cojanuteodor/Voltage-Regulator-with-Series-Pass-Element/Simulations/DOMENIU_DE_TEMP_LA_VO_MAX.png

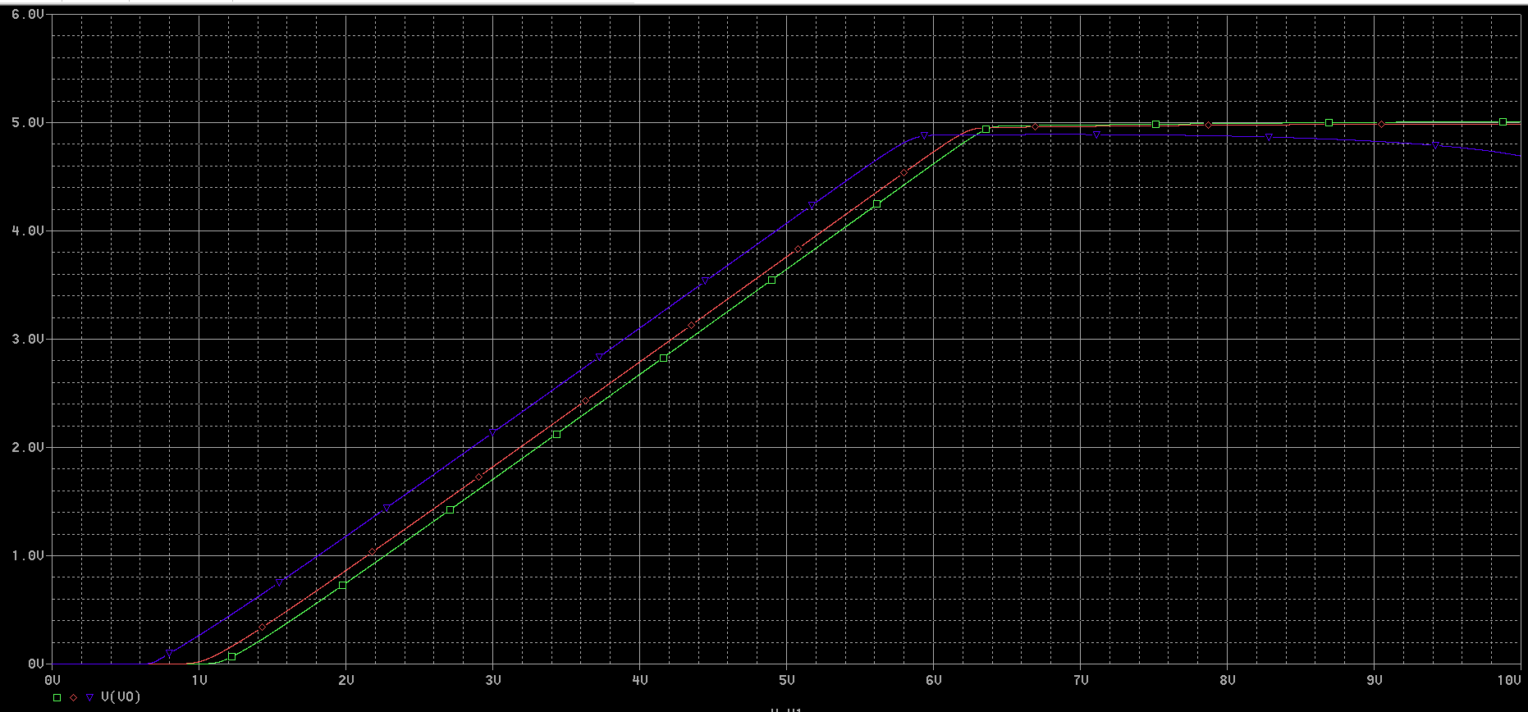
Simulations/DOMENIU_DE_TEMP_LA_VO_MAX.png
