cojanuteodor/Voltage-Regulator-with-Series-Pass-Element/Simulations/DOMENIU_DE_TEMP_VO_MIN.png

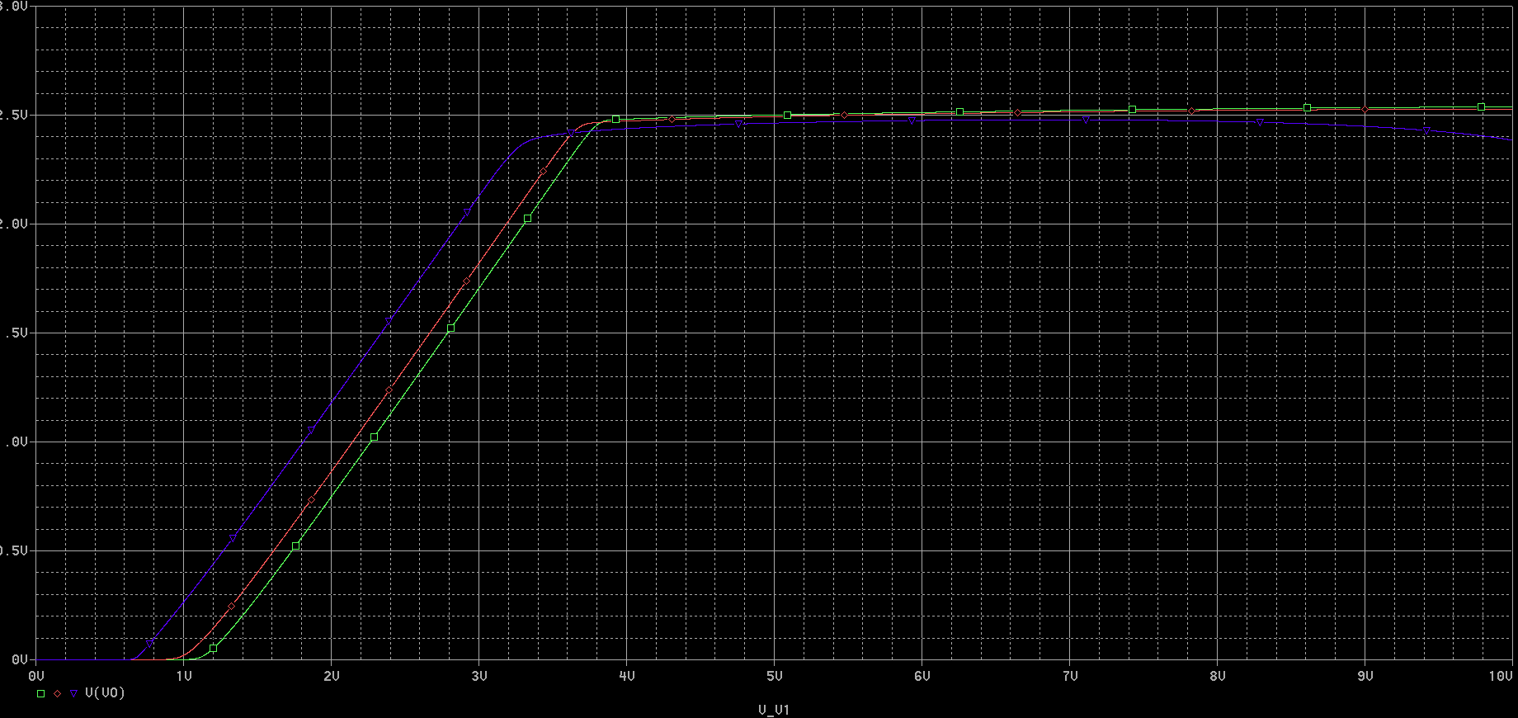
Simulations/DOMENIU_DE_TEMP_VO_MIN.png
