cojanuteodor/Voltage-Regulator-with-Series-Pass-Element/Simulations/PROTECTIA_TERMICA_LA_VO_MIN.png

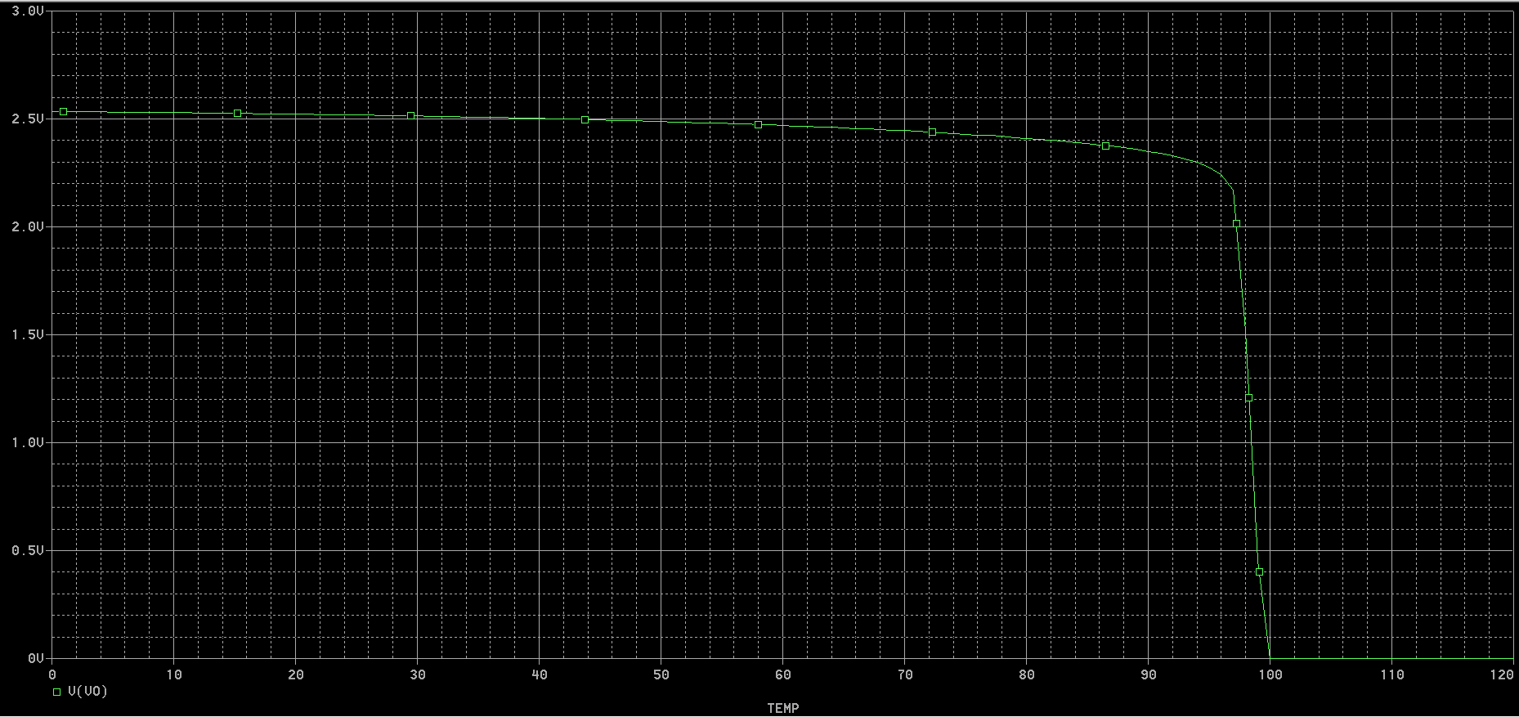
Simulations/PROTECTIA_TERMICA_LA_VO_MIN.png
