cojanuteodor/Voltage-Regulator-with-Series-Pass-Element/Simulations/PROTECTIA_TERMICA_VO_MAX.png

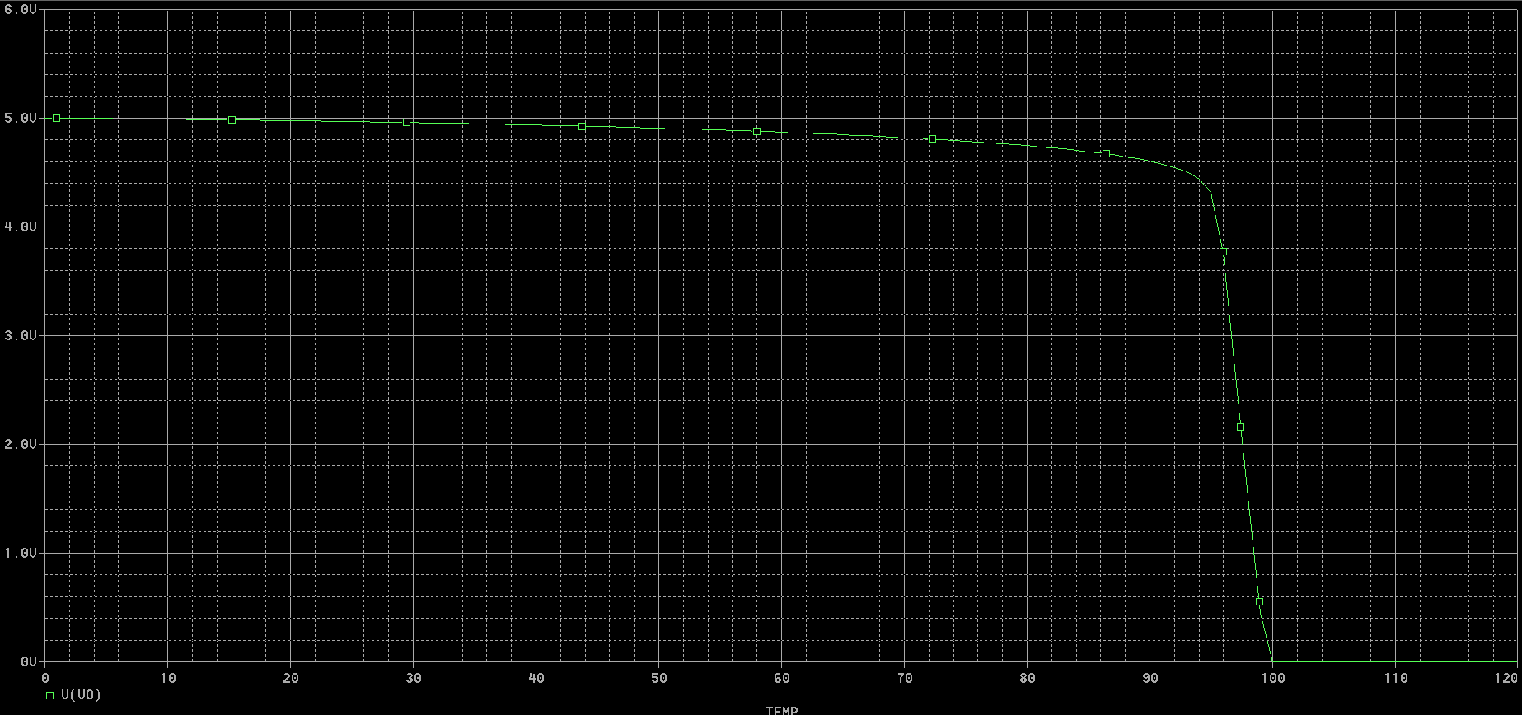
Simulations/PROTECTIA_TERMICA_VO_MAX.png
