cojanuteodor/Voltage-Regulator-with-Series-Pass-Element/Simulations/STABILIZARE_LA_VO_MAX.png

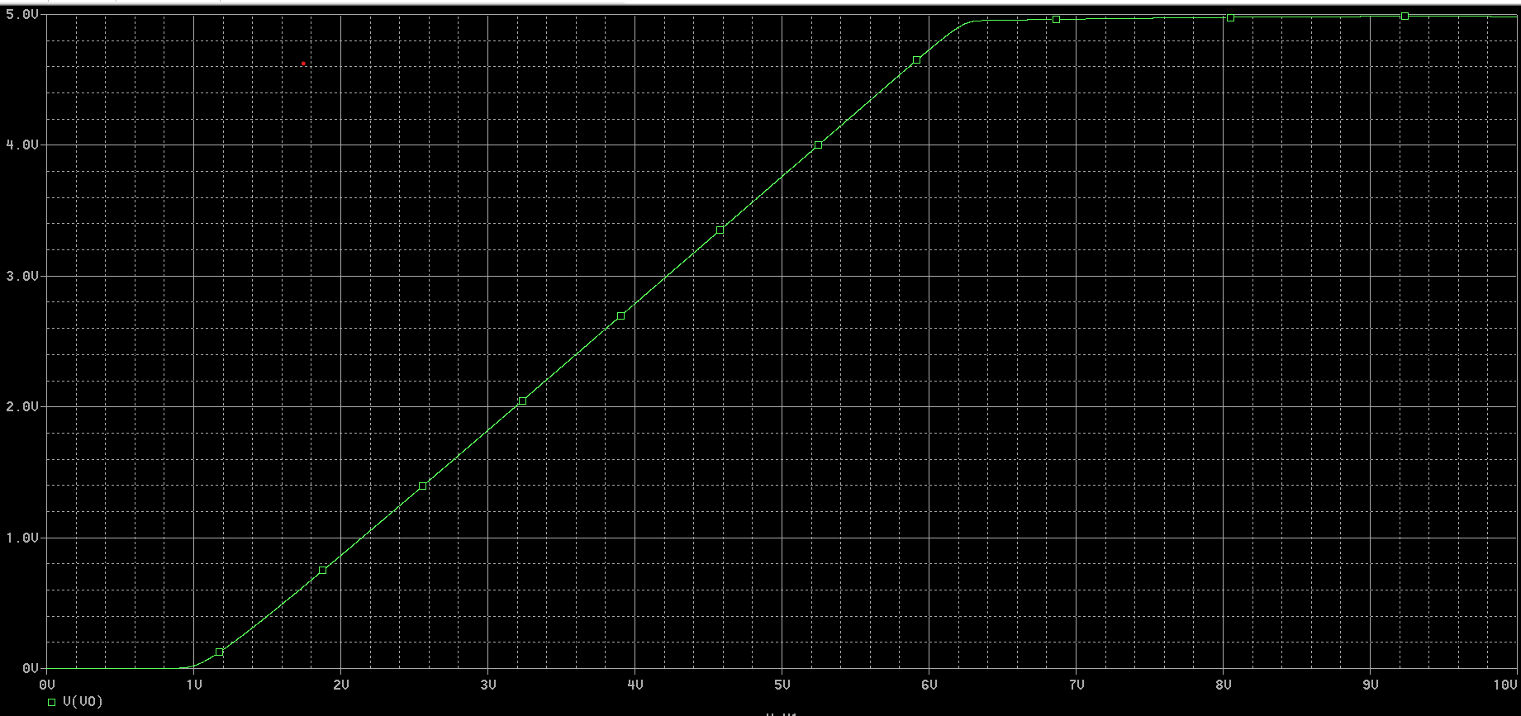
Simulations/STABILIZARE_LA_VO_MAX.png
